220-gruppe/varierende_psu/main/include/tempsensor.h

#ifndef TEMPS_H
#define TEMPS_H

#include <DFRobot_MLX90614.h>
#include <Wire.h>

extern DFRobot_MLX90614_I2C sensor;  
extern float AVG_TEMP;

void setupTempSensor();
float takeTempMeasurement();    

#endif  
