220-gruppe/varierende_psu/main/include/logo.h

#ifndef LOGO_H
#define LOGO_H

#include <Arduino.h>

static const uint16_t logo[] PROGMEM = {
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
};

#endif
