220-gruppe/varierende_psu/main/include/numpad.cpp

#include "numpad.h"
#include "screen.h"

namespace
{
    Adafruit_MPR121 numpad = Adafruit_MPR121();
    String typed = "";
    bool userDone = false;

    void applyTypedPreview()
    {
        screenPinPreview(typed);
    }

    void clearTypedInput()
    {
        typed = "";
        userDone = false;
        applyTypedPreview();
    }
}

void setupNumpad()
{
    if (!numpad.begin(0x5A, &Wire))
    {
        Serial.println("STOP! MPR121 ikke fundet.");
        while (1)
        {
            delay(10);
        }
    }

    Serial.println("Den er fundet makker");
    numpad.setAutoconfig(true);
    applyTypedPreview();
}

String getTyped()
{
    return typed;
}

bool isUserDone()
{
    return userDone;
}

void resetNumpad()
{
    clearTypedInput();
}

namespace
{
    NumpadOverride overrideCallback = nullptr;
}

void setNumpadOverride(NumpadOverride callback)
{
    overrideCallback = callback;
}

void numpadLogik()
{
    uint16_t numpadValue = numpad.touched();
    if (numpadValue == 0)
    {
        return;
    }

    int activeBit = -1;
    for (uint8_t i = 0; i < 12; i++)
    {
        if (numpadValue & _BV(i))
        {
            activeBit = i;
            break;
        }
    }

    if (activeBit == -1)
    {
        return;
    }

    String value = "";
    bool clearRequested = false;
    bool enterRequested = false;

    switch (activeBit)
    {
    case 7:
        if (overrideCallback && overrideCallback(7))
            break;
        value = "0";
        break;
    case 0:
        if (overrideCallback && overrideCallback(0))
            break;
        value = "1";
        break;
    case 4:
        value = "2";
        break;
    case 8:
        value = "3";
        break;
    case 1:
        value = "4";
        break;
    case 5:
        value = "5";
        break;
    case 9:
        value = "6";
        break;
    case 2:
        value = "7";
        break;
    case 6:
        value = "8";
        break;
    case 10:
        value = "9";
        break;
    case 3:
        if (overrideCallback && overrideCallback(3))
            break;
        clearRequested = true;
        break;
    case 11:
        if (overrideCallback && overrideCallback(11))
            break;
        enterRequested = true;
        break;
    default:
        return;
    }

    if (clearRequested)
    {
        clearTypedInput();
        Serial.print("SLET");
    }
    else if (value.length() > 0)
    {
        if (typed.length() < 4)
        {
            typed += value;
            userDone = false;
            applyTypedPreview();
            Serial.print(value + " ");
        }
    }

    if (enterRequested && typed.length() > 0)
    {
        userDone = true;
        Serial.println("#");
    }

    delay(250);
}
