220-gruppe/varierende_psu/main/include/svejse_logs.h

#ifndef SVEJSE_LOGS_H
#define SVEJSE_LOGS_H

#include <Arduino.h>

enum class SvejsningStatus
{
    Approved = 0,
    NotApproved = 1
};

float calculatedOutputEnergy();
float getTargetEnergy();
bool wasApproved();
void saveSvejsningResult();
bool writeSvejseLog(const String &svejsningResult,
                    const String &calculatedEnergy,
                    const String &avgTemp,
                    float svejsningTime);
void LogSvejseData();

#endif 
